neuroidss/FreeEEG128-alpha/KiCAD/out/kicad_pcb/FreeEEG128-alpha_kicad_pcb.png

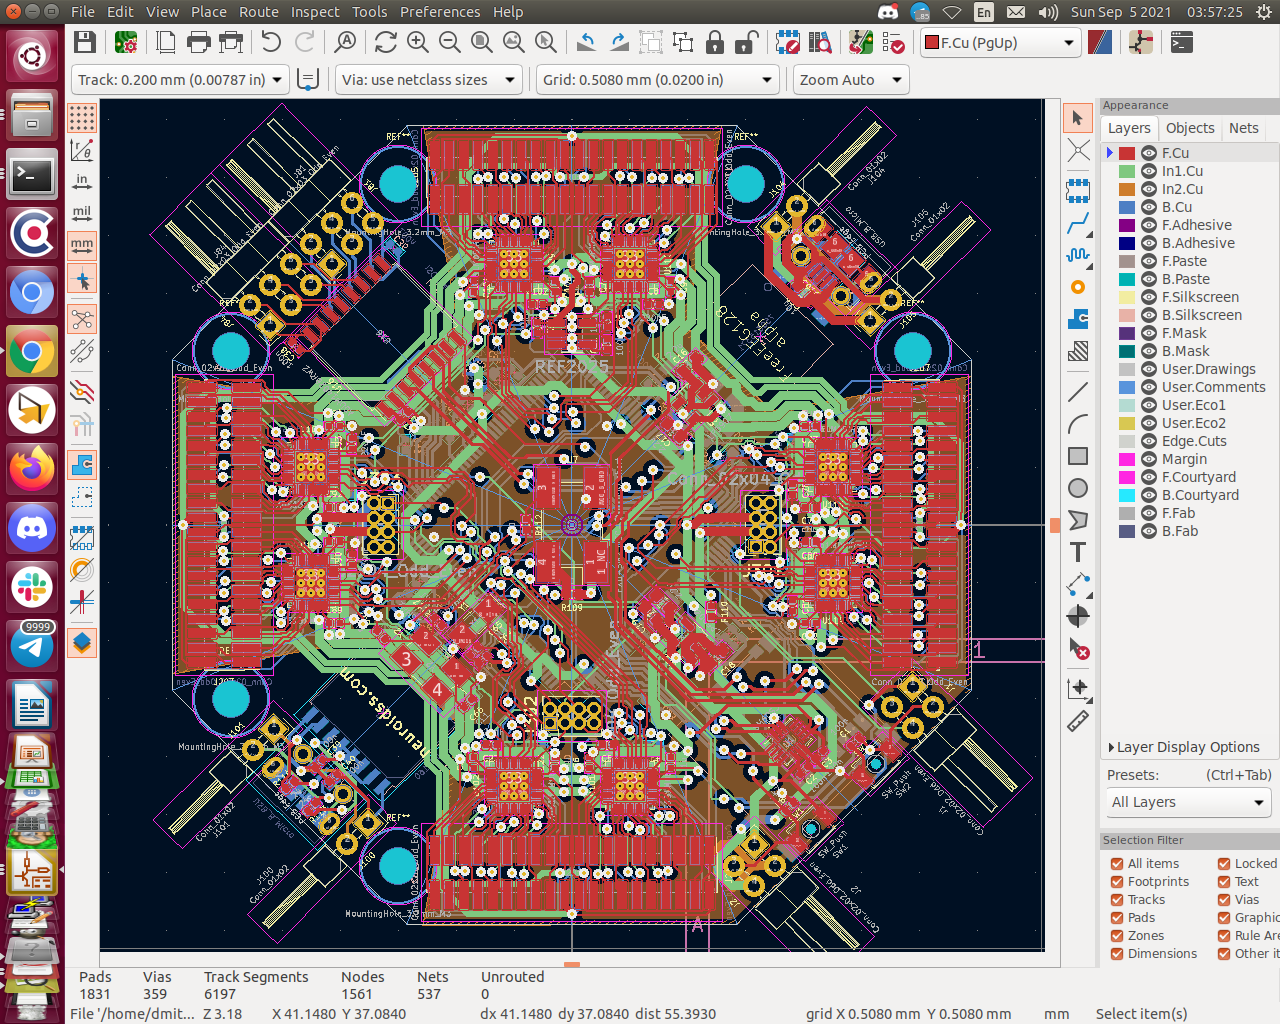
KiCAD/out/kicad_pcb/FreeEEG128-alpha_kicad_pcb.png
